AngelArzuaga/amplificador-op-bjt/ltspice/amp-op-bjt-buffer.asc

C1: cap; 100nF
Q1: npn; 2N3904
Q2: npn; 2N3904
Q3: npn; 2N3904
Q4: npn; 2N3904
Q5: pnp; 2N3906
Q6: npn; 2N3904
Q7: pnp; 2N3906
Q8: pnp; 2N3906
Rref1: res; 10k
Vcc1: voltage; 5
VIN: voltage; SINE(2 0.03 1k)
Named nets: 0, VEE, vb2, vb1, Vref
.tran 0.01
