AngelArzuaga/amplificador-op-bjt/ltspice/amp-op-bjt-feedback.asc

C1: cap; 100nF
Q1: npn; 2N3904
Q2: npn; 2N3904
Q3: npn; 2N3904
Q4: npn; 2N3904
Q5: pnp; 2N3906
Q6: npn; 2N3904
Q7: pnp; 2N3906
Q8: pnp; 2N3906
R1: res; 1k
R2: res; 1k
Rref1: res; 10k
V1: voltage; 2
Vcc1: voltage; 5
VIN: voltage; SINE(2 0.03 1k); AC 1
Named nets: 0, VEE, out, vb2, vb1, Vref, Vf
.ac dec 10 1 1meg
